foxlox/notco2_arduino/docs/PCB/schema.jpg

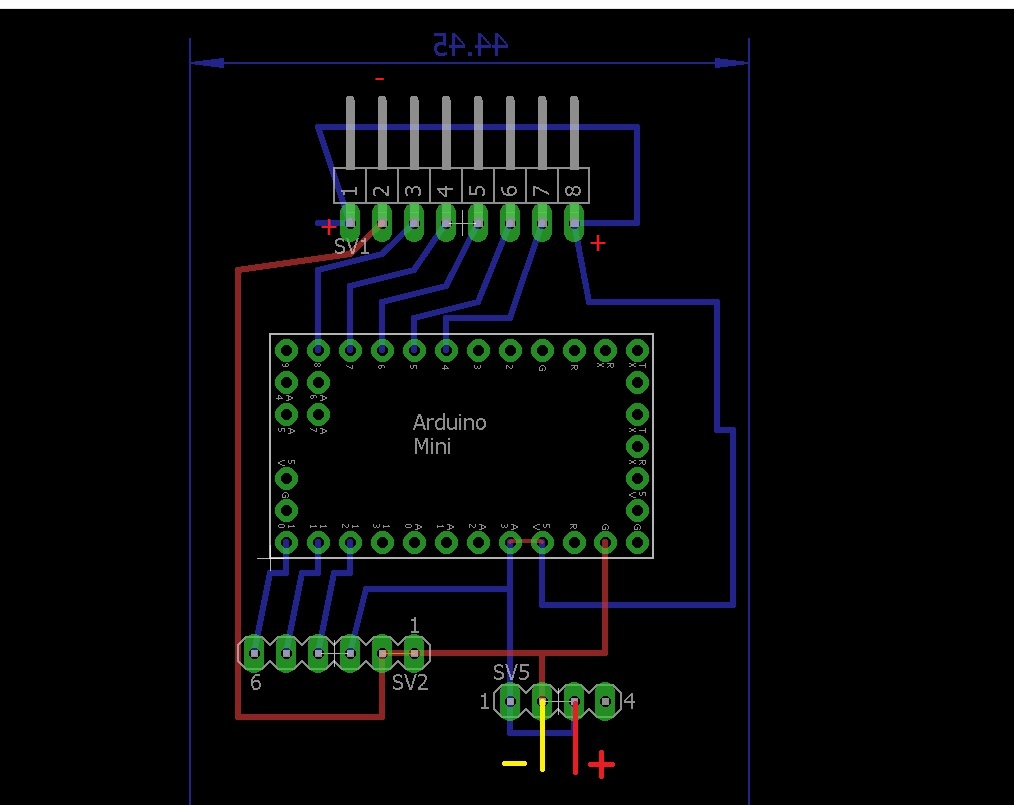
docs/PCB/schema.jpg
