foxlox/notco2_arduino/docs/zzz_pics/8_leds_module.png

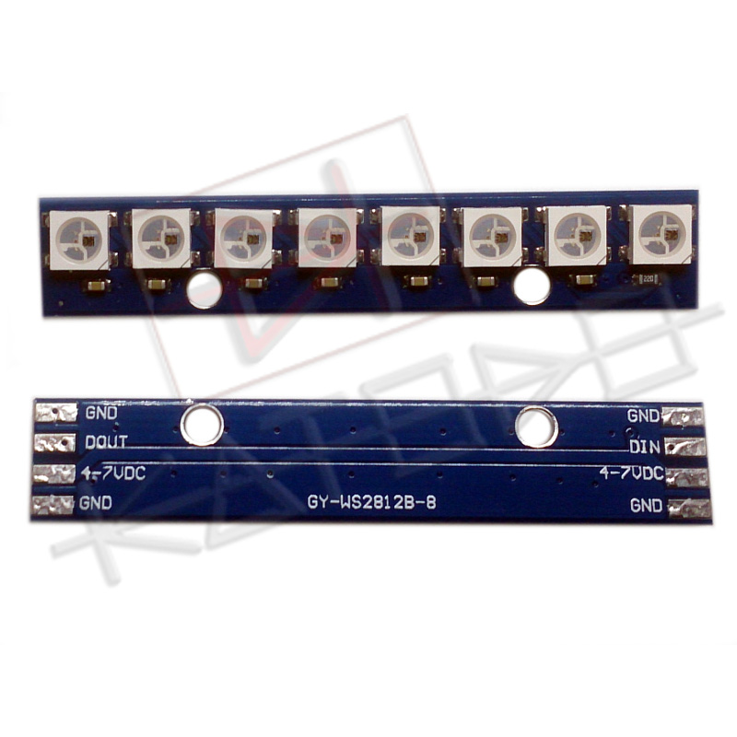
docs/zzz_pics/8_leds_module.png
