foxlox/notco2_arduino/docs/zzz_pics/2014-03-23 15.53.34.jpg

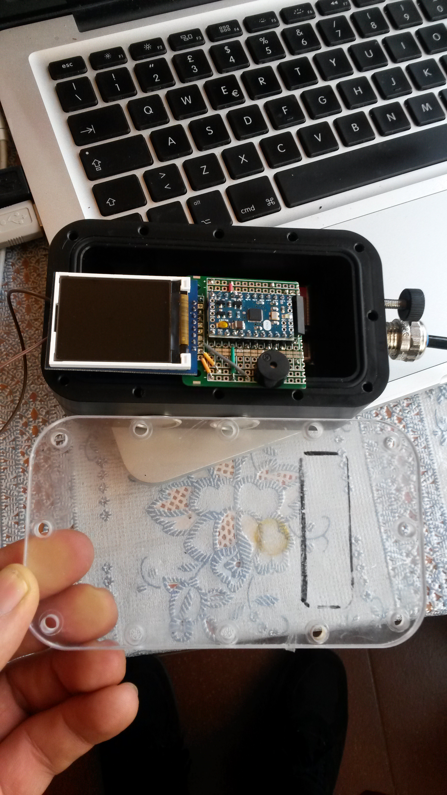
docs/zzz_pics/2014-03-23 15.53.34.jpg
