foxlox/notco2_arduino/docs/zzz_pics/20131202_074404.jpg

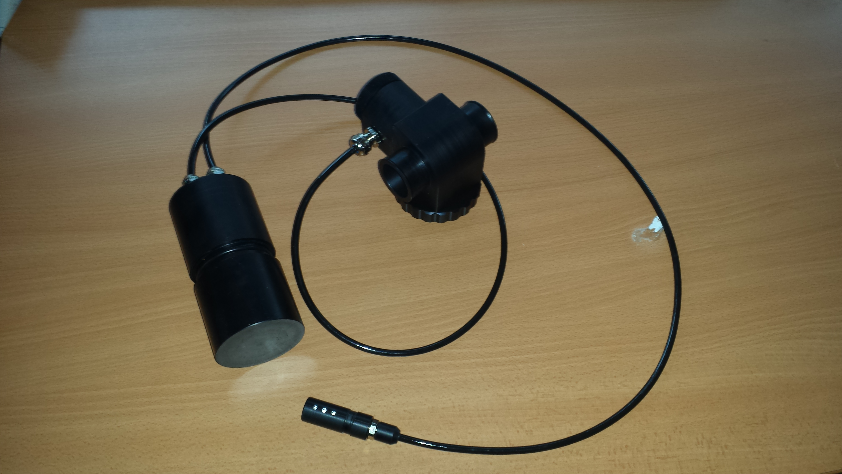
docs/zzz_pics/20131202_074404.jpg
