foxlox/notco2_arduino/docs/zzz_pics/buddy.jpg

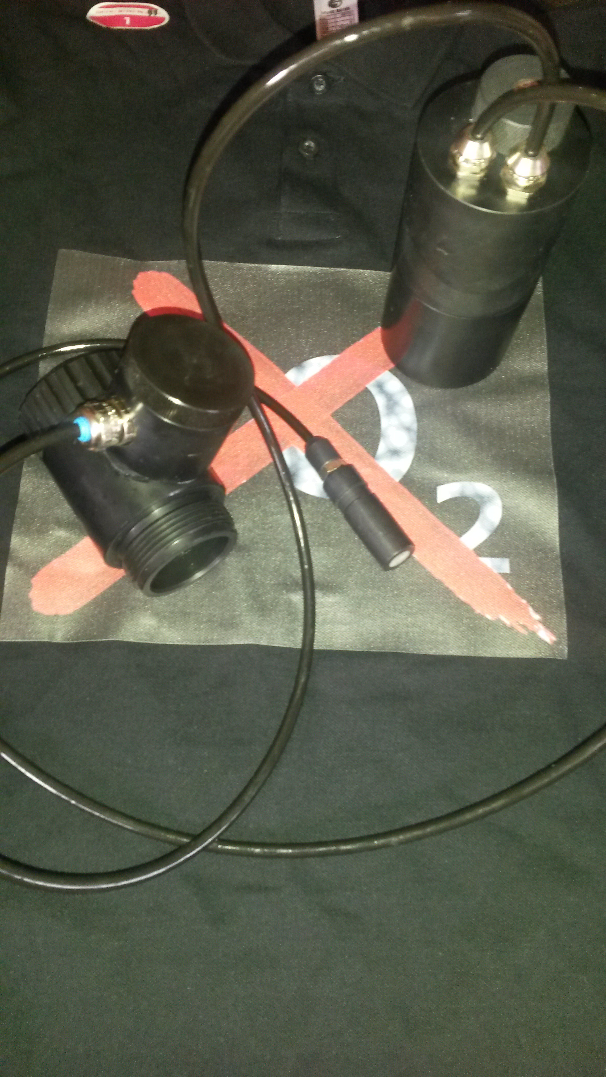
docs/zzz_pics/buddy.jpg
