foxlox/notco2_arduino/docs/zzz_pics/co2_1.jpg

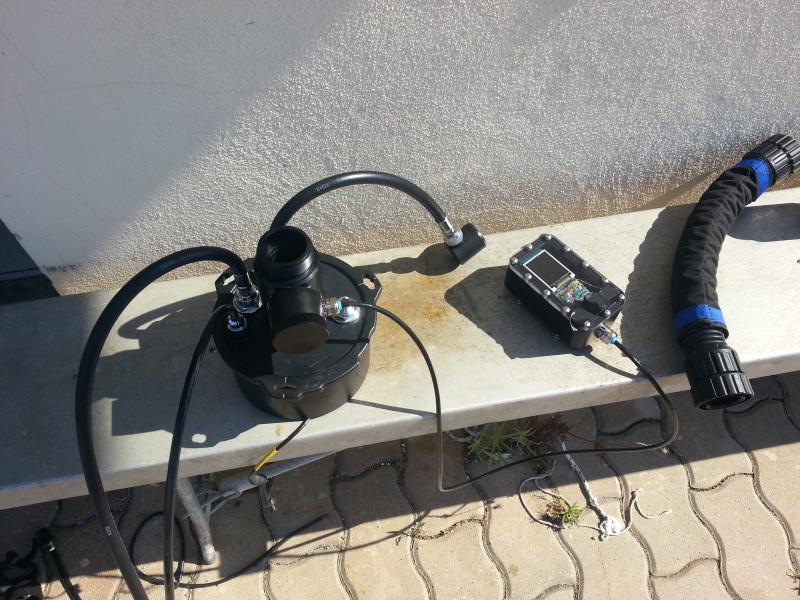
docs/zzz_pics/co2_1.jpg
