foxlox/notco2_arduino/docs/zzz_pics/console_sebastiano_pappalardo.jpg

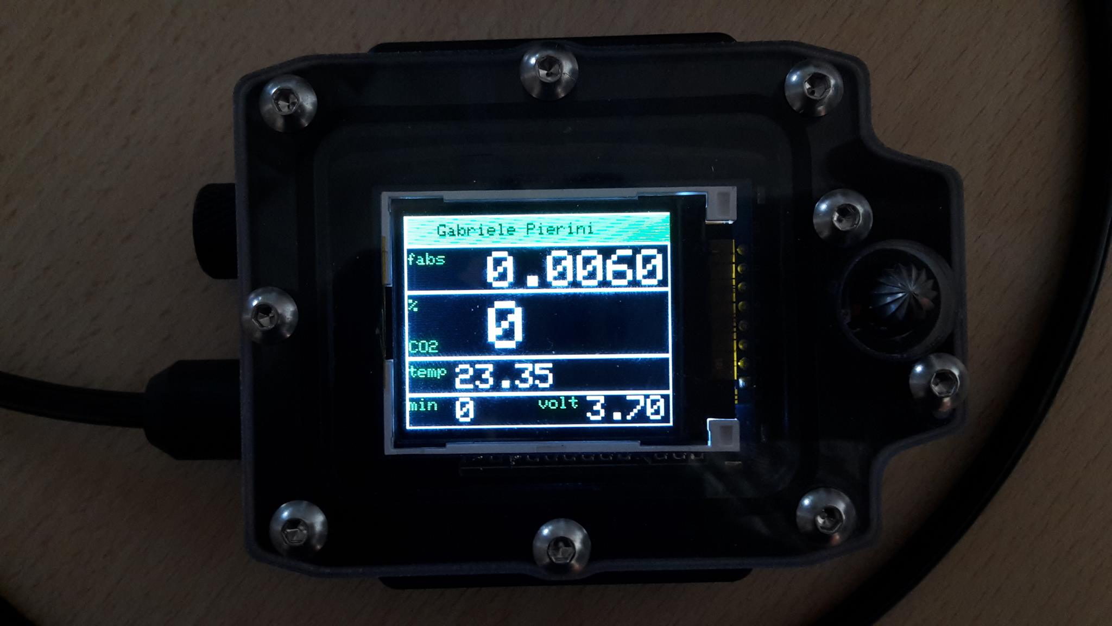
docs/zzz_pics/console_sebastiano_pappalardo.jpg
