foxlox/notco2_arduino/docs/zzz_pics/enclosure_meg_tecme.jpg

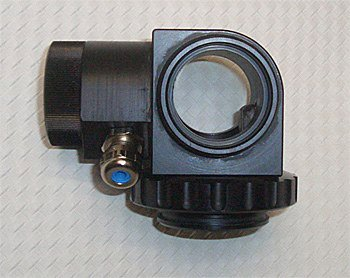
docs/zzz_pics/enclosure_meg_tecme.jpg
