foxlox/notco2_arduino/docs/zzz_pics/enclosure_poseidon_tecme.jpg

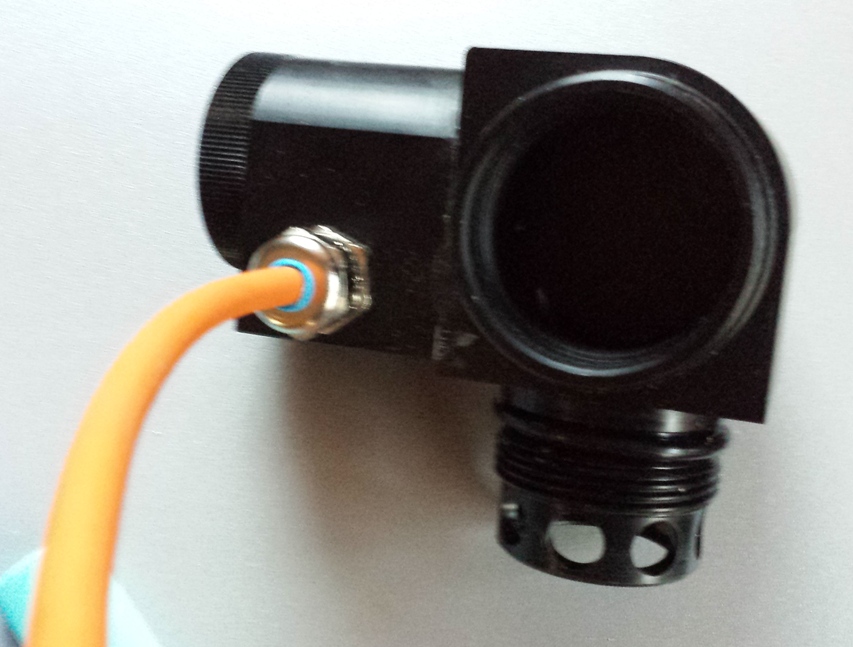
docs/zzz_pics/enclosure_poseidon_tecme.jpg
