foxlox/notco2_arduino/docs/zzz_pics/meg_tecme.jpg

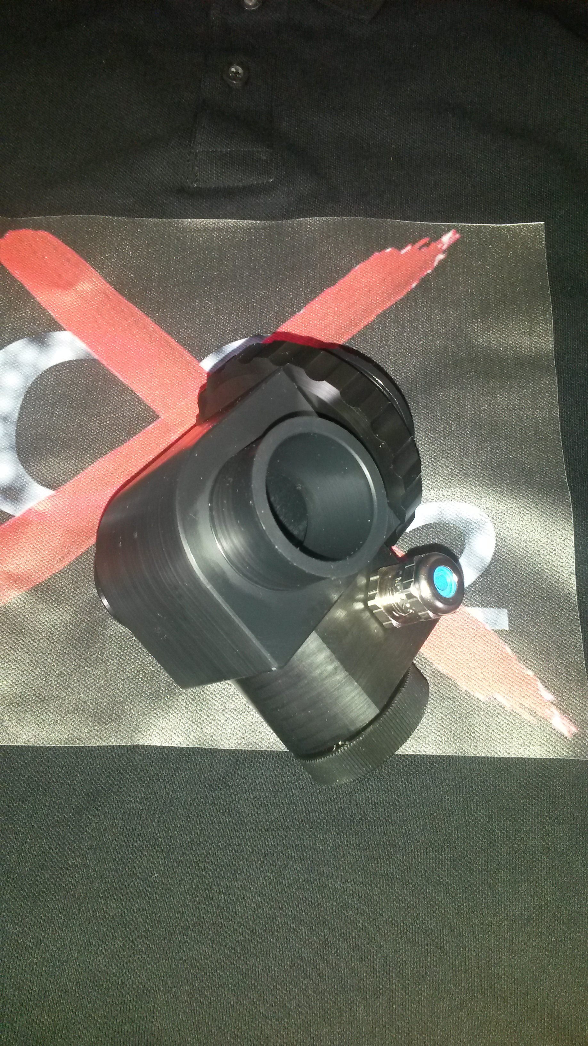
docs/zzz_pics/meg_tecme.jpg
