foxlox/notco2_arduino/docs/zzz_pics/Poseidon_mk7_tecme.jpg

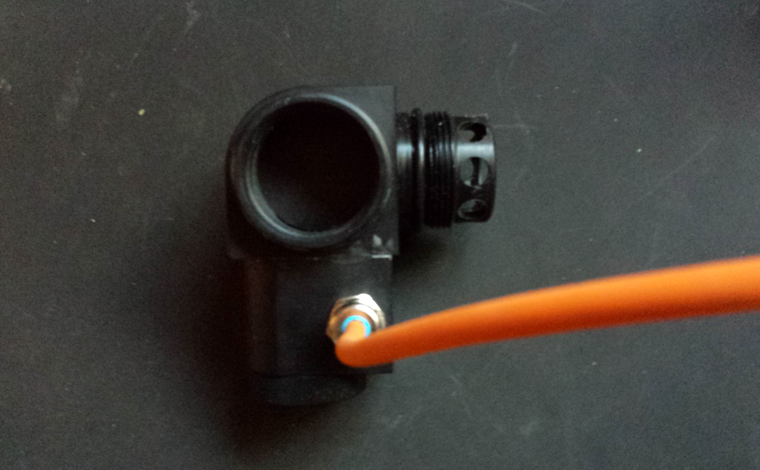
docs/zzz_pics/Poseidon_mk7_tecme.jpg
