foxlox/notco2_arduino/docs/zzz_pics/Poseidon_Sebastiano.jpg

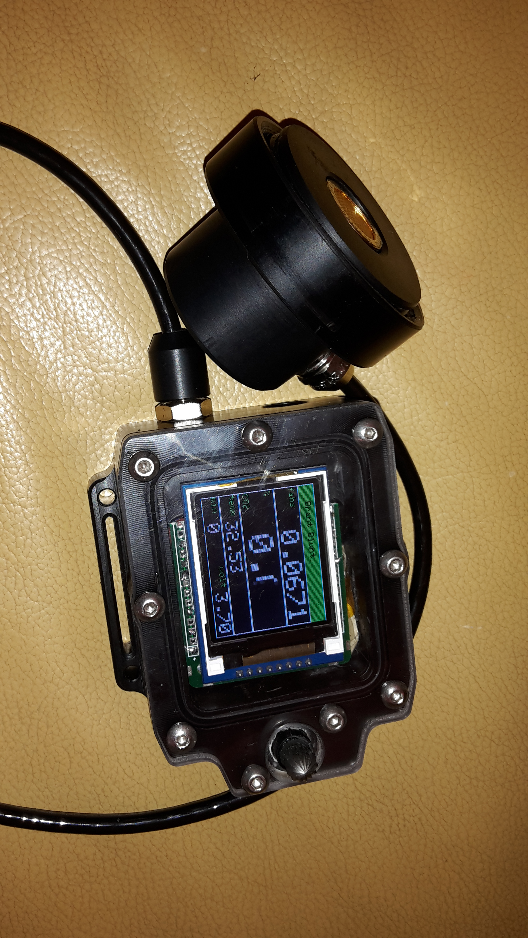
docs/zzz_pics/Poseidon_Sebastiano.jpg
