foxlox/notco2_arduino/docs/zzz_pics/Poseidon_Sebastiano_2.jpg

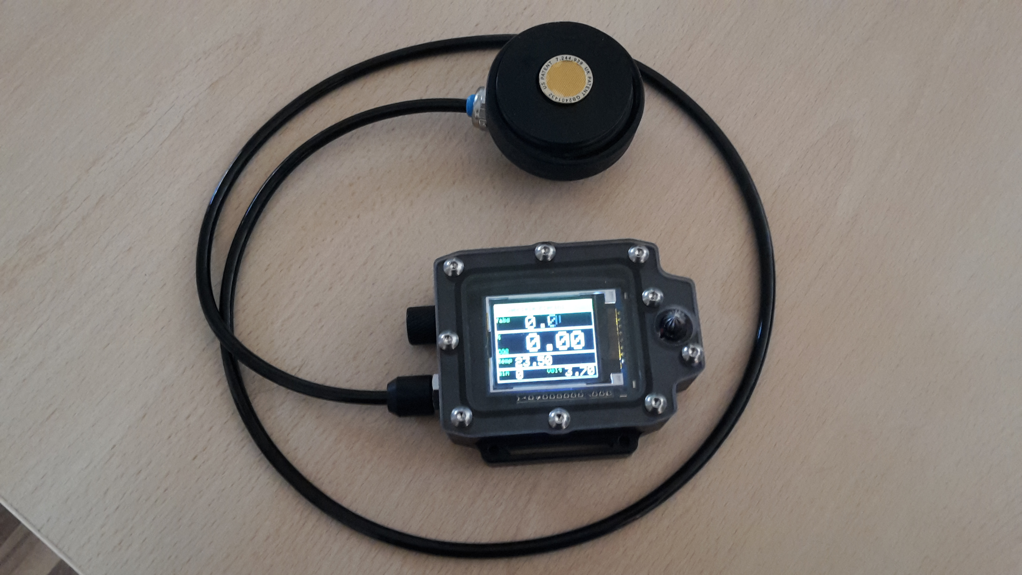
docs/zzz_pics/Poseidon_Sebastiano_2.jpg
