foxlox/notco2_arduino/docs/zzz_pics/sensor_enclosures_meg_tecme.jpg

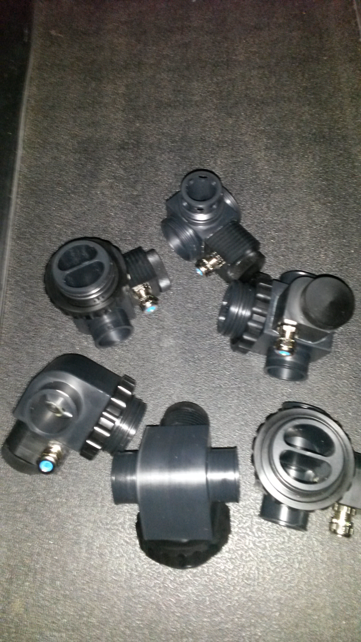
docs/zzz_pics/sensor_enclosures_meg_tecme.jpg
