foxlox/notco2_arduino/docs/zzz_pics/sensor_with_PCB.jpg

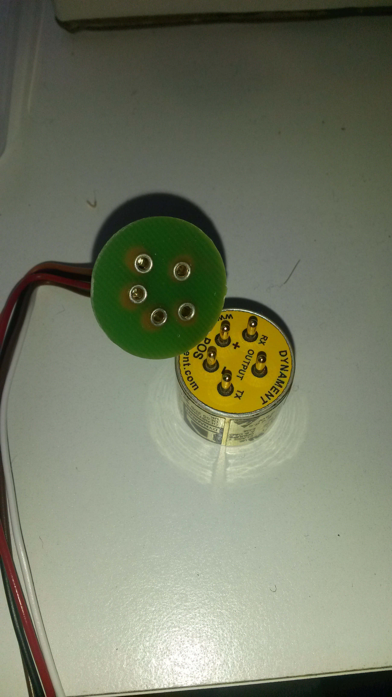
docs/zzz_pics/sensor_with_PCB.jpg
