foxlox/notco2_arduino/docs/zzz_pics/universal_sensor_enclosure_tecme_3.jpg

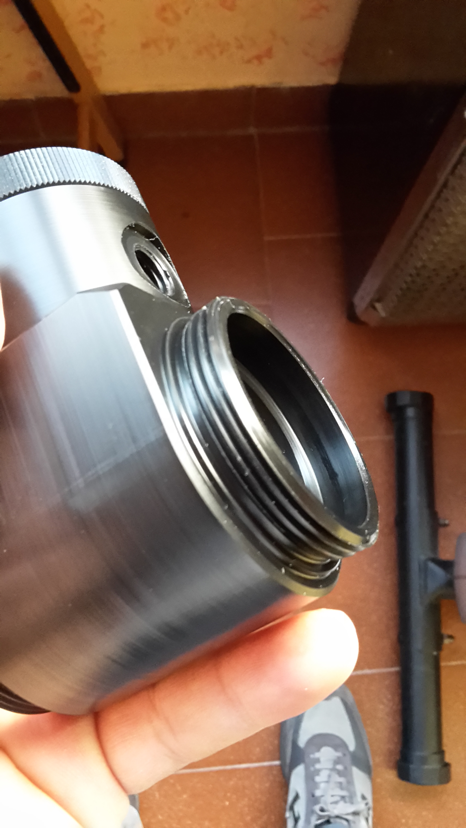
docs/zzz_pics/universal_sensor_enclosure_tecme_3.jpg
