foxlox/notco2_arduino/docs/zzz_pics/wrist_enclosure_Sebastiano_2.jpg

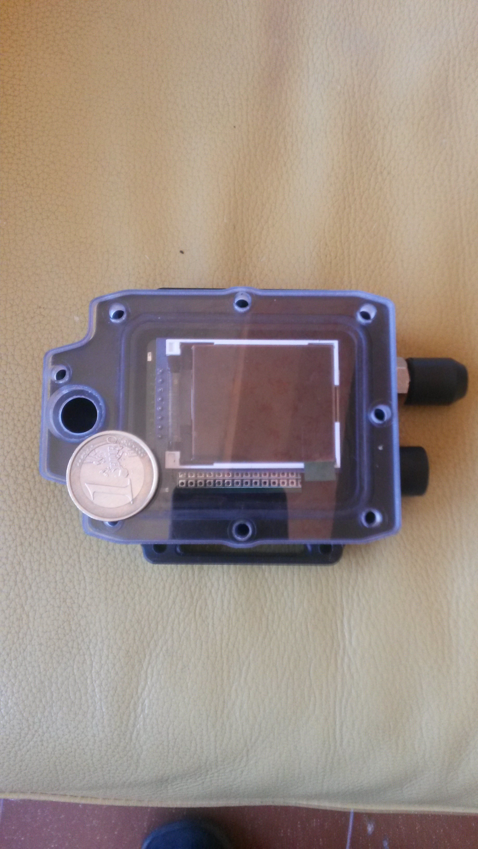
docs/zzz_pics/wrist_enclosure_Sebastiano_2.jpg
