foxlox/notco2_arduino/docs/zzz_pics/wrist_enclosure_Sebastiano_3.jpg

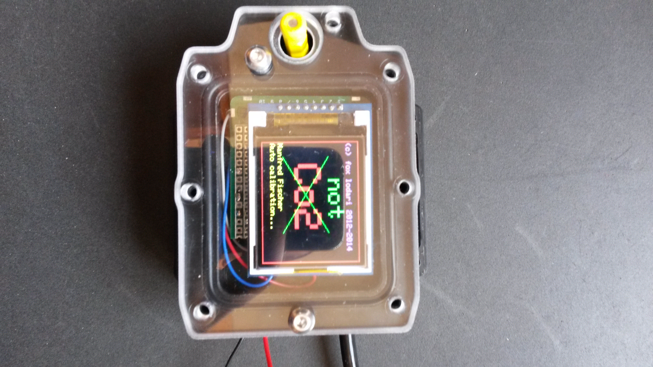
docs/zzz_pics/wrist_enclosure_Sebastiano_3.jpg
